AlekPnv/wedding-pos-terminal/images/product/buttons.jpg

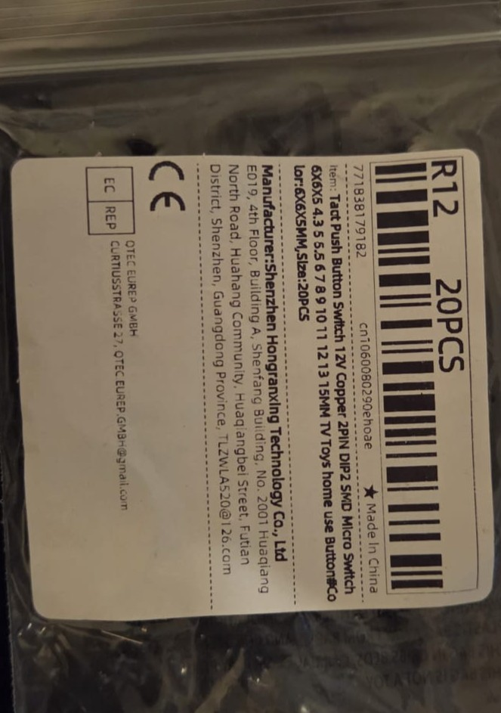
images/product/buttons.jpg
