AlekPnv/wedding-pos-terminal/images/product/buzzer.jpg

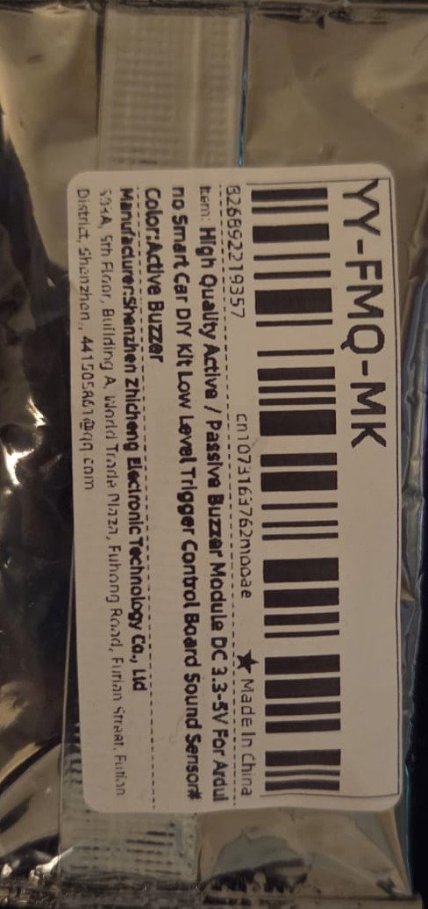
images/product/buzzer.jpg
