AlekPnv/wedding-pos-terminal/images/product/cables.jpg

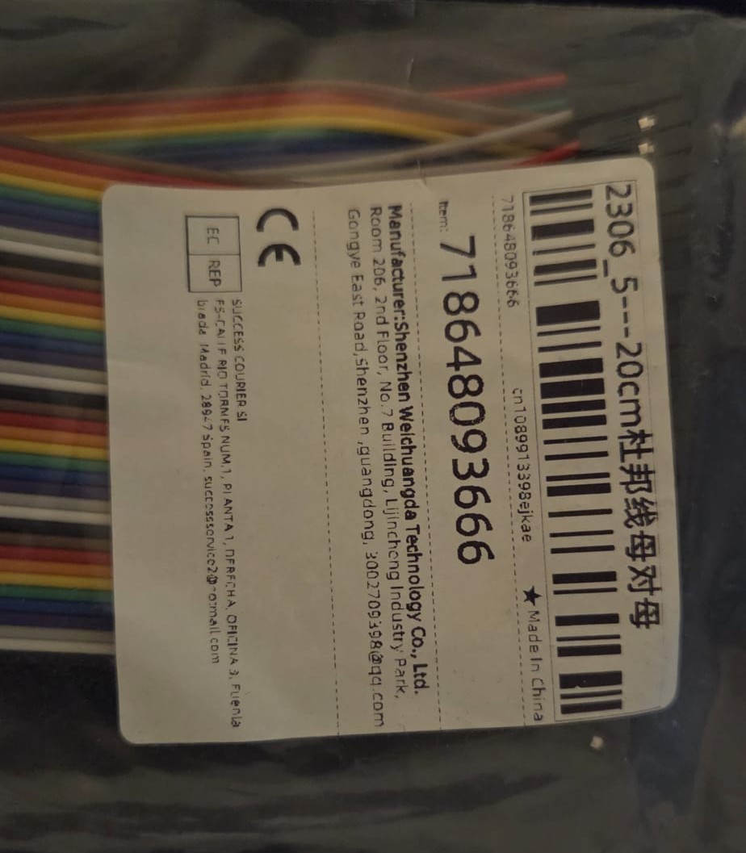
images/product/cables.jpg
