AlekPnv/wedding-pos-terminal/images/product/heatsink.jpg

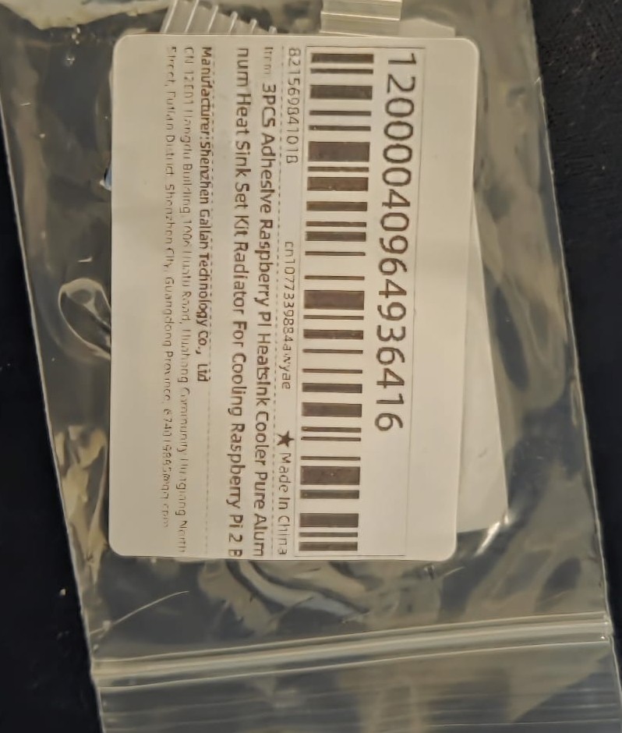
images/product/heatsink.jpg
