AlekPnv/wedding-pos-terminal/images/product/oled.jpg

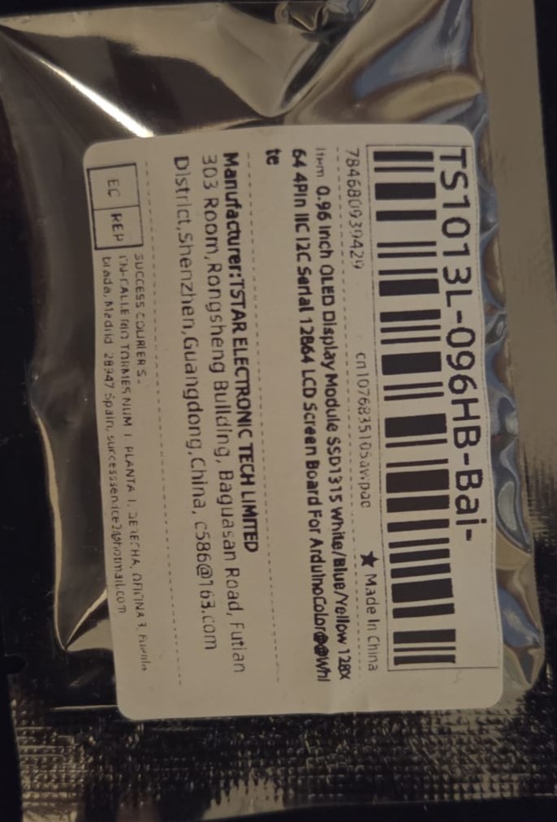
images/product/oled.jpg
