AlekPnv/wedding-pos-terminal/images/product/usb_switch.jpg

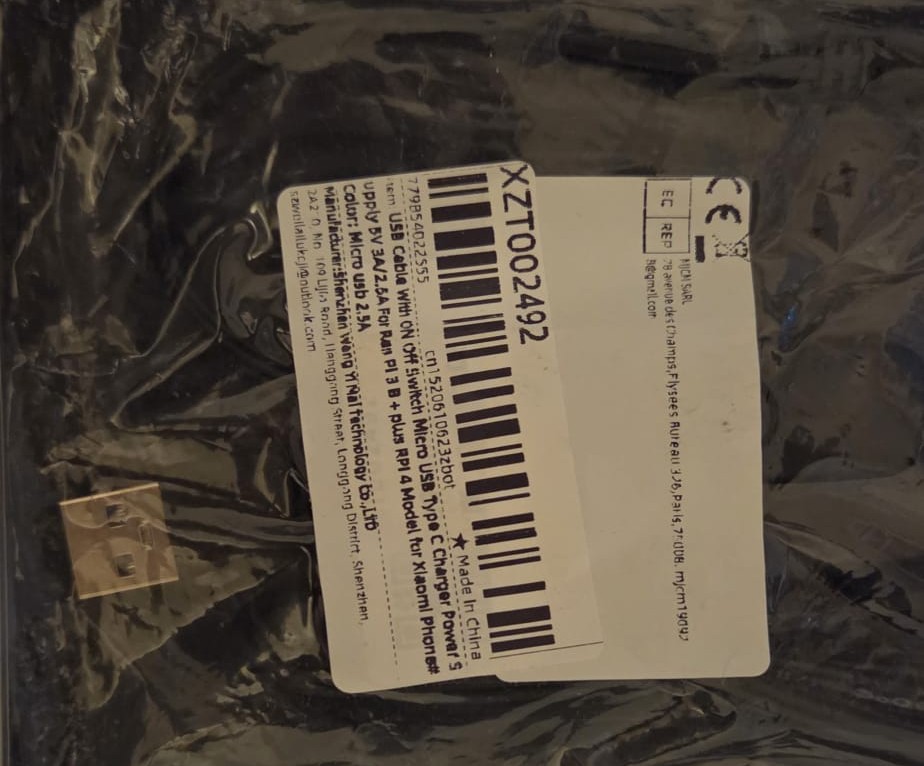
images/product/usb_switch.jpg
