AlekPnv/wedding-pos-terminal/images/build/07_buttons_wiring.jpg

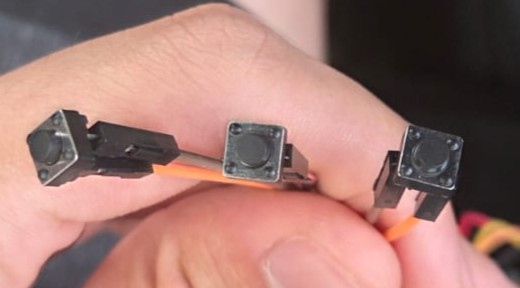
images/build/07_buttons_wiring.jpg
