AlekPnv/wedding-pos-terminal/images/build/09_pi_back.jpg

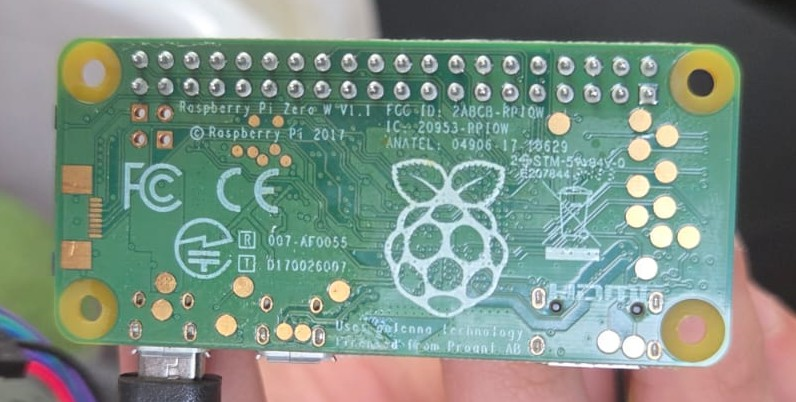
images/build/09_pi_back.jpg
